gawainhewitt/piezo_signal_conditioner/piezo_signal_conditioner/piezo_signal_conditioner.kicad_sch

## KiCad design piezo_signal_conditioner/piezo_signal_conditioner.kicad_sch (2026-03-13, an earlier design)

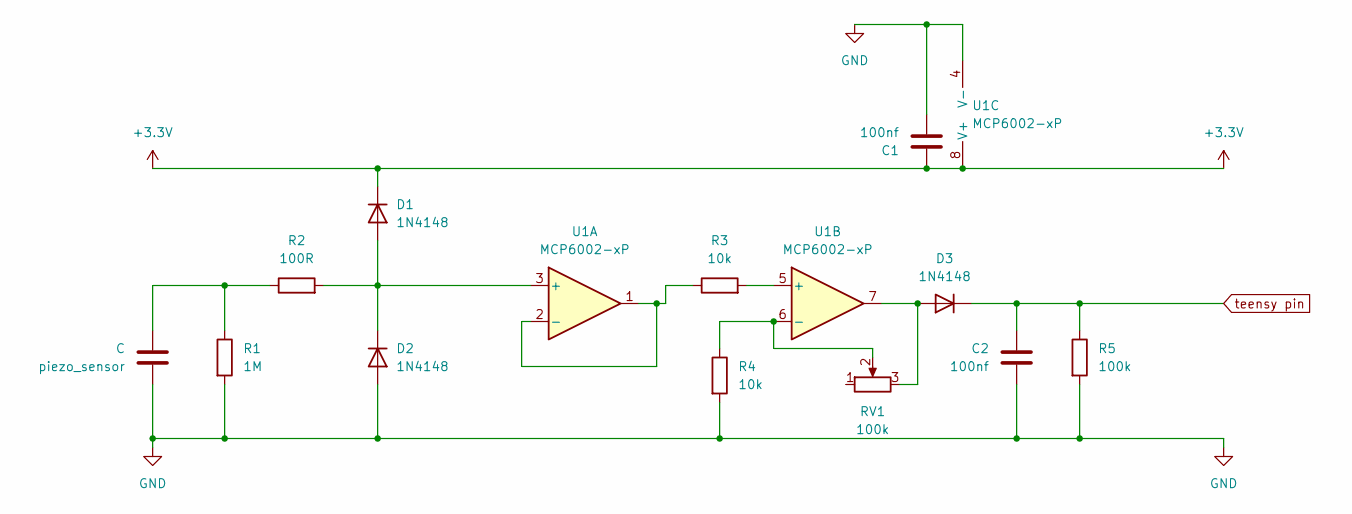
[picture p7: schematic piezo_signal_conditioner.kicad_sch]

Parts:
C1, C2: 100nf
D1, D2, D3: 1N4148; D_DO-35_SOD27_P7.62mm_Horizontal
R1: 1M
R2: 100R
R3, R4: 10k
R5: 100k
RV1: 100k
U1: MCP6002-xP
piezo_sensor: C

Connections:
+3.3V: C1.2, D1.1 (K), U1.8 (V+)
GND: C1.1, C2.2, D2.2 (A), R1.2, R4.2, R5.2, U1.4 (V-), piezo_sensor.1
unnamed: D1.2 (A), D2.1 (K), R2.2, U1.3 (+)
unnamed: D3.2 (A), RV1.3, U1.7
unnamed: R1.1, R2.1, piezo_sensor.2
unnamed: R3.1, U1.1, U1.2 (-)
unnamed: R3.2, U1.5 (+)
unnamed: R4.1, RV1.2, U1.6 (-)
teensy pin: C2.1, D3.1 (K), R5.1
